tamago324/split-mini/rev0.13/swtich_plate__L.dxf

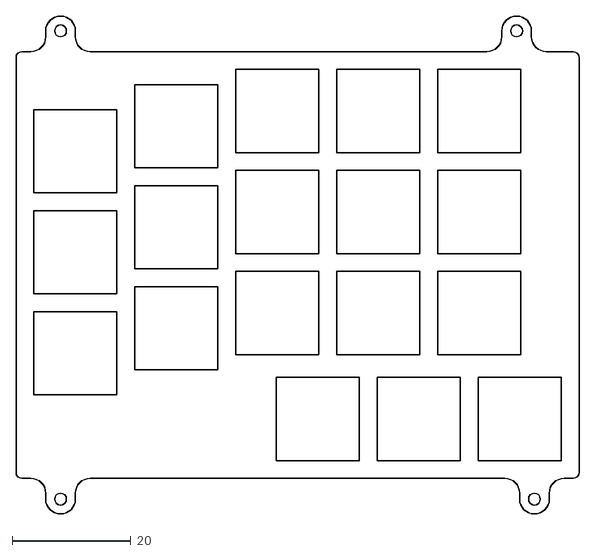
[picture p36: CAD file, 2023-02-03]
rev0.13/swtich_plate__L.dxf
94.8 x 83.9
